SwissElectron/CAN-Motor-Control-Board/Images/FrontLayer.png

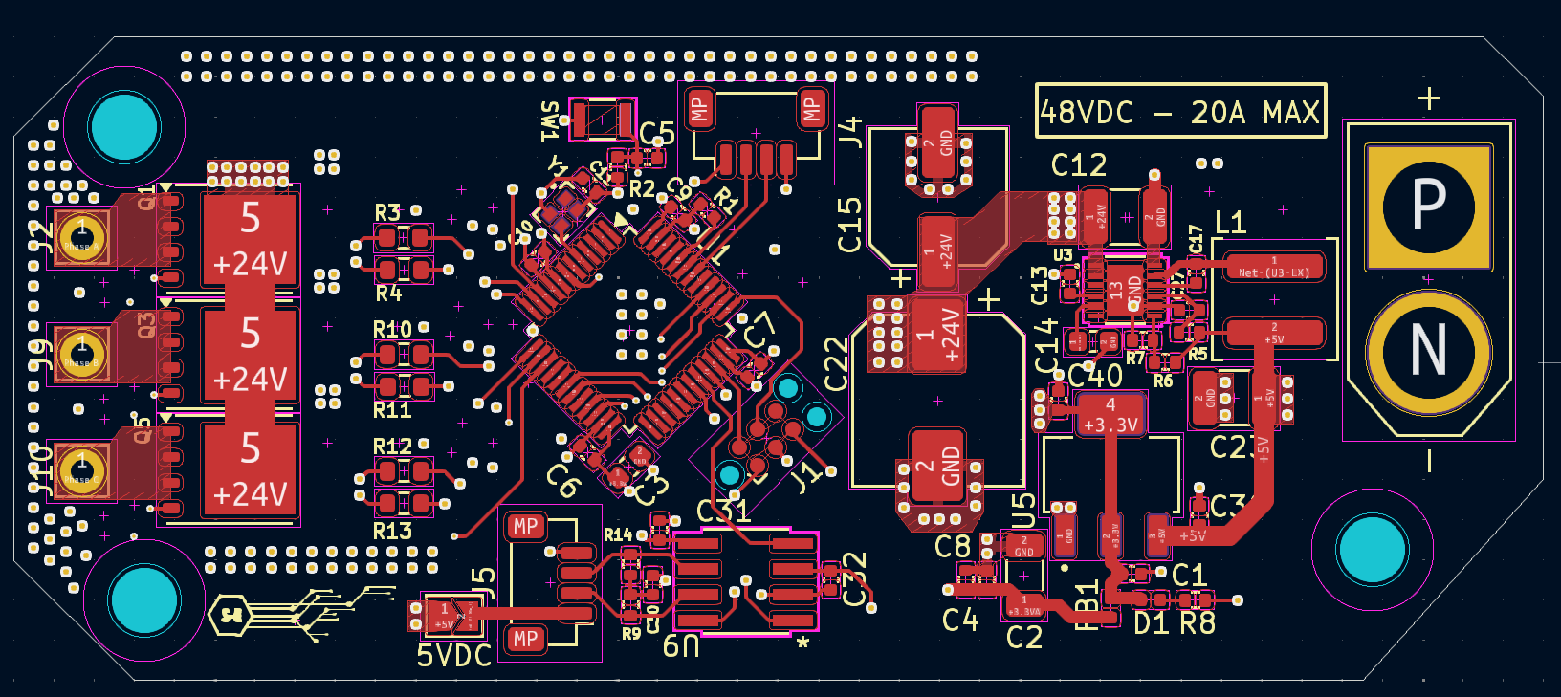
Images/FrontLayer.png
