SwissElectron/CAN-Motor-Control-Board/Images/MotorDriver.png

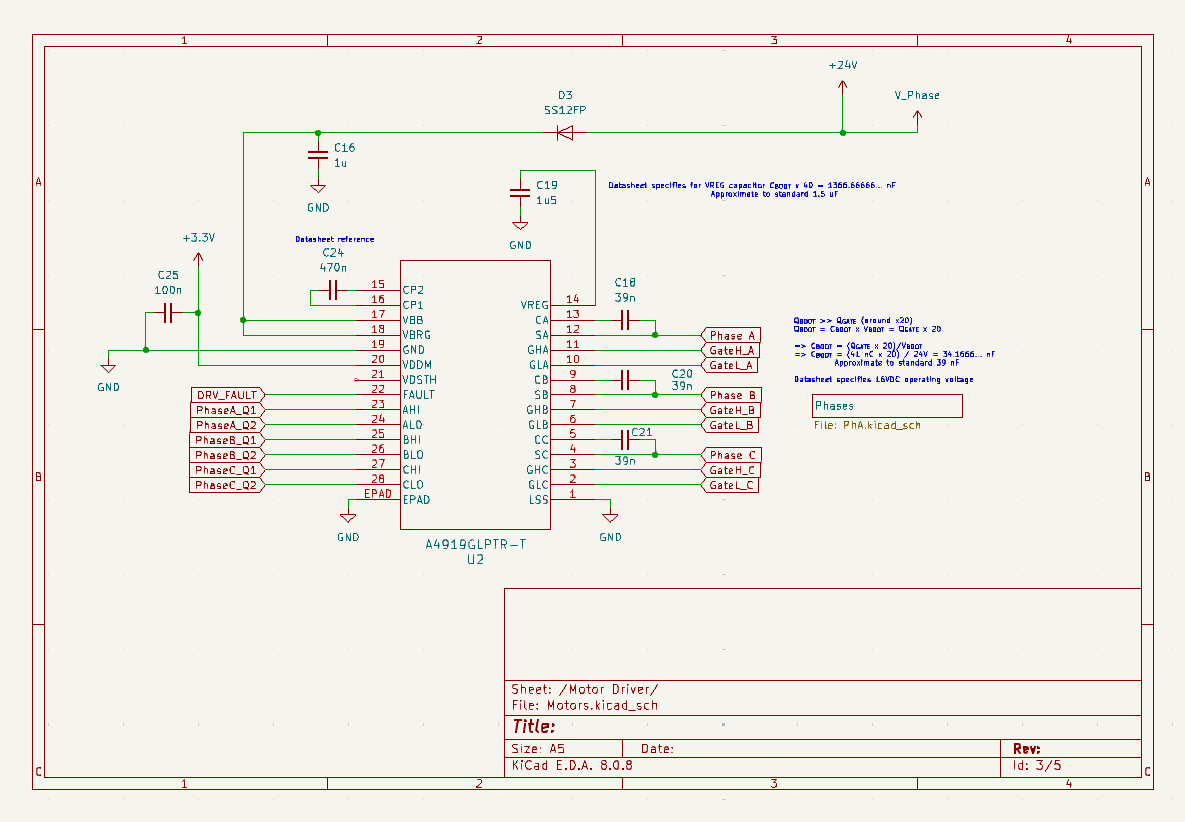
Images/MotorDriver.png
